ryanredbaron/UV-Watch/SunSensor_Firmware/V1-Motion_Testing/V1-Motion_Testing.ino

// Accel Test

// Accelerometer routines (in separate tab)

//bool accelBegin(bool shakeMode, uint8_t shakeThreshold, uint8_t shakeCount, uint8_t orientationCount);
//int accelX();         Get raw X value
//int accelY();         Get raw Y value
//int accelZ();         Get raw Z value
//uint8_t accelXYZT();  Get orientation (directions and signs

#include <tinyNeoPixel.h>
#include "TinyI2CMaster.h"

// Which pin on the Arduino is connected to the NeoPixels?
#define NEO_PIN PIN_PA3

// How many NeoPixels are attached to the Arduino?
#define NUMPIXELS 12
tinyNeoPixel pixels = tinyNeoPixel(NUMPIXELS, NEO_PIN, NEO_GRB + NEO_KHZ800);

#define I2C_WRITE 0

// Deprecated (will be going away but still working)
extern void accelRead();
extern bool orientDisplay();
extern void getShake();
// Deprecated Accel global values (will be going away but still working)
uint16_t aOrient;
uint16_t aShake;
uint16_t notMoving = 0;

// Globals

uint8_t gotAccel = 0;
uint8_t lefthanded = 0;

#define ON 50
#define OFF 0
uint8_t red = OFF;
uint8_t green = OFF;
uint8_t blue = OFF;

uint8_t nled;

int PreviousX;
int CurrentX;

int PreviousY;
int CurrentY;

int PreviousZ;
int CurrentZ;

void setup() {
  Serial.begin(115200);

  TinyI2C.init();  // Not in the library desc.!! Only in examples...
  pixels.begin();  // Initializes tinyNeoPixel library.
  pixels.setBrightness(25);

  // Don't worry about initialization values now (don't affect basic operation)
  // bool shakeMode, uint8_t shakeThreshold, uint8_t shakeCount, uint8_t orientationCount
  gotAccel = accelBegin(0, 0, 0, 0);

  for (int i = 0; i < NUMPIXELS; i++) {
    pixels.setPixelColor(i, pixels.Color(OFF, ON, OFF));
    delay(1);
  }
  pixels.show();
}

int SensorCaptureTimer = 0;
int SensorCaptureTrigger = 10;

int DisplayTimer = 0;
int DisplayTimerTrigger = 500;

int MoCapTimer = 0;
int MoCapTimerTrigger = 1;

int TapCount;

void loop() {
  SensorCaptureTimer++;
  DisplayTimer++;
  MoCapTimer++;

#define Xbit 0b00001000
#define Ybit 0b00000100
#define Zbit 0b00000010
#define Tbit 0b00000001

  //-----------------------------Motion CAPTURE---------------------------------------
  if (MoCapTimer >= MoCapTimerTrigger) {
    uint8_t xyzt = accelXYZT();

    PreviousX = CurrentX;
    CurrentX = accelX();
    int DeltaX = CurrentX - PreviousX;

    PreviousY = CurrentY;
    CurrentY = accelY();
    int DeltaY = CurrentY - PreviousY;

    PreviousZ = CurrentZ;
    CurrentZ = accelZ();
    int DeltaZ = CurrentZ - PreviousZ;

    int XYTrigger = 250;
    int ZTrigger = -250;

    if (CurrentZ < 0 && DeltaZ < ZTrigger && (DeltaX < XYTrigger && DeltaX > (XYTrigger * -1)) && (DeltaY < XYTrigger && DeltaY > (XYTrigger * -1))) {
      TapCount++;
      DisplayTimer = 0;
    }

    MoCapTimer = 0;
  }
  //----------------------------------------------------------------------------------



  //-----------------------------SENSOR CAPTURE---------------------------------------
  if (SensorCaptureTimer >= SensorCaptureTrigger) {

    SensorCaptureTimer = 0;
  }
  //--------------------------------------------------------------------


  //-------------------------------DISPLAY-------------------------------------
  if (DisplayTimer >= DisplayTimerTrigger) {
    for (int i = 0; i < NUMPIXELS; i++) {
      if (i < TapCount && TapCount > 0) {
        pixels.setPixelColor(i, pixels.Color(OFF, ON, ON));
      } else {
        pixels.setPixelColor(i, pixels.Color(OFF, OFF, OFF));
      }
      delay(1);
    }
    pixels.show();
    TapCount = 0;

    DisplayTimer = 0;
  }
  //--------------------------------------------------------------------

  delay(1);
}
